DriftingOtter/Project-Resonator/BA Driver Spec Sheets/Knowles_BK_26824/Frequency_Response.png

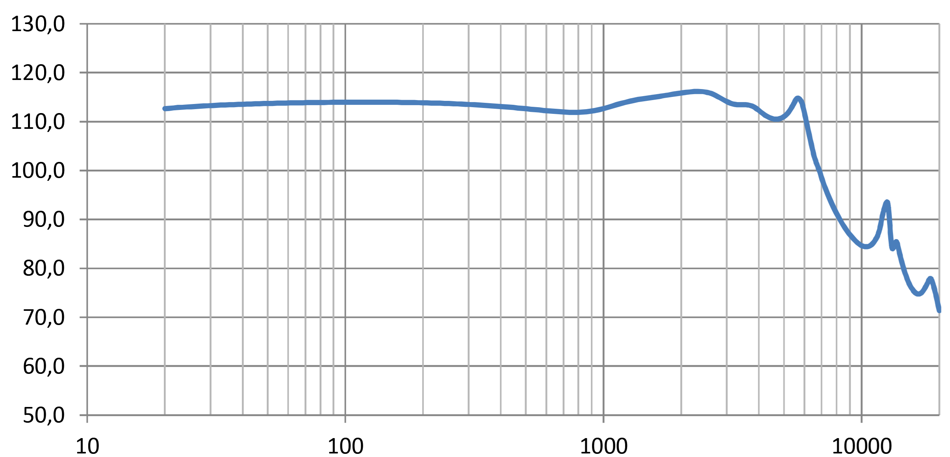
BA Driver Spec Sheets/Knowles_BK_26824/Frequency_Response.png
