DriftingOtter/Project-Resonator/BA Driver Spec Sheets/Knowles_CI_22955/Frequnecy_Response.png

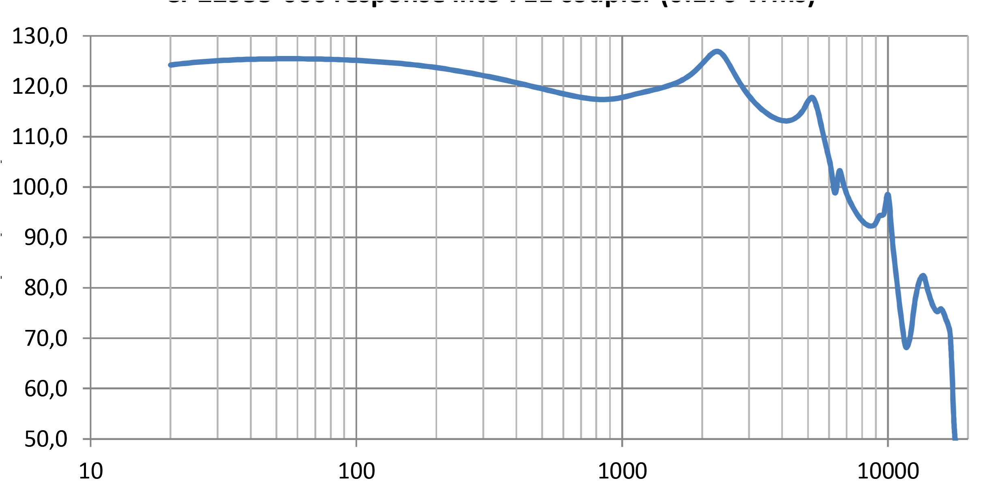
BA Driver Spec Sheets/Knowles_CI_22955/Frequnecy_Response.png
