DriftingOtter/Project-Resonator/BA Driver Spec Sheets/Knowles_CI_22955/Impedence_Response.png

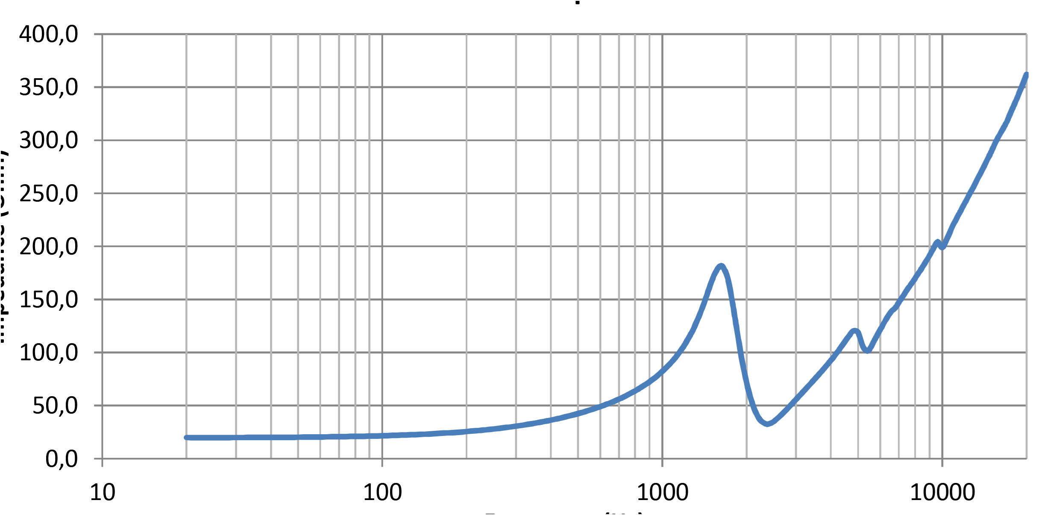
BA Driver Spec Sheets/Knowles_CI_22955/Impedence_Response.png
