DriftingOtter/Project-Resonator/BA Driver Spec Sheets/Knowles_ED_30262/Frequnecy_Response.png

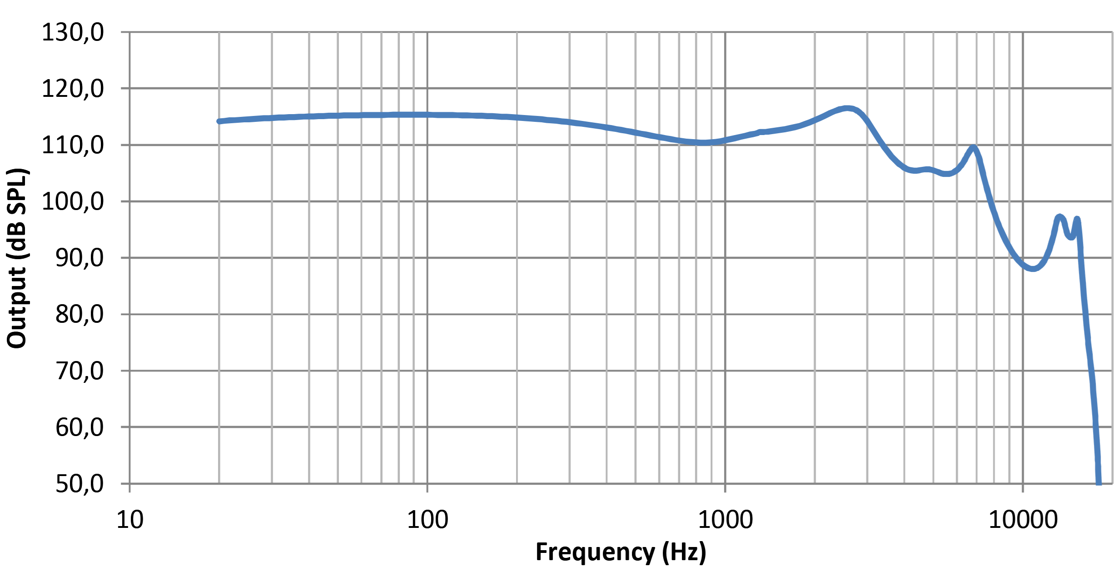
BA Driver Spec Sheets/Knowles_ED_30262/Frequnecy_Response.png
