DriftingOtter/Project-Resonator/BA Driver Spec Sheets/Knowles_HODVTEC-31618/Impedence_Response.png

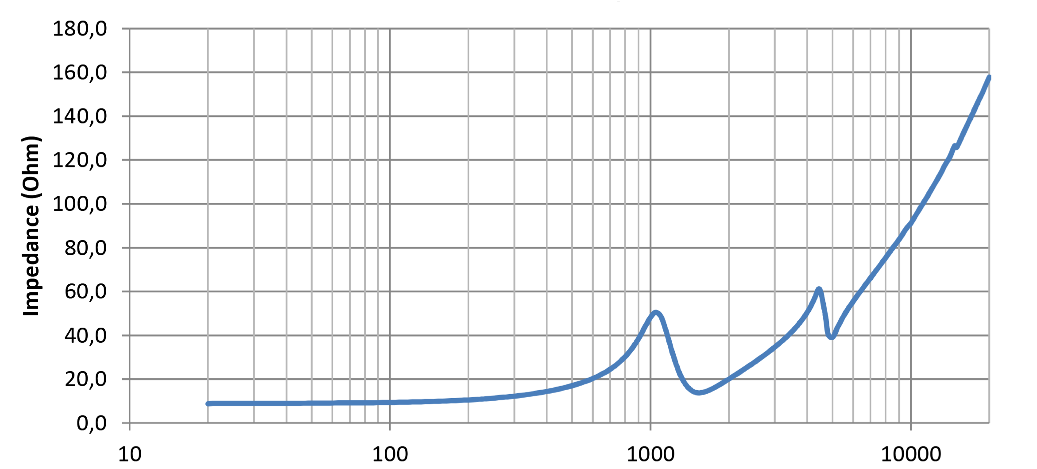
BA Driver Spec Sheets/Knowles_HODVTEC-31618/Impedence_Response.png
