DriftingOtter/Project-Resonator/BA Driver Spec Sheets/Knowles_RDI_34006/Frequnecy_Response.png

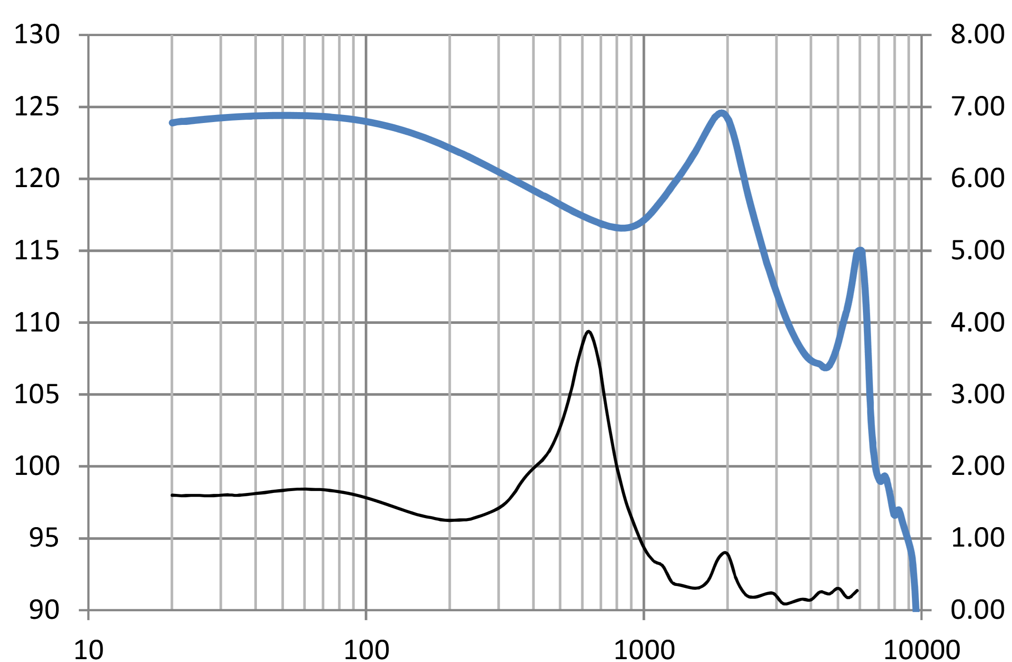
BA Driver Spec Sheets/Knowles_RDI_34006/Frequnecy_Response.png
