DriftingOtter/Project-Resonator/BA Driver Spec Sheets/Knowles_SR6438NWS/Frequnecy_Response.png

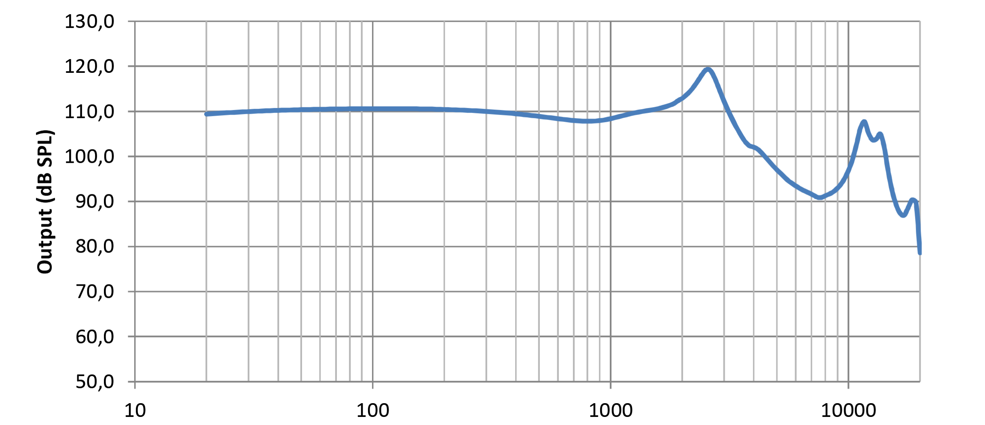
BA Driver Spec Sheets/Knowles_SR6438NWS/Frequnecy_Response.png
