DriftingOtter/Project-Resonator/BA Driver Spec Sheets/Knowles_TEC_30033/Frequnecy_Response.png

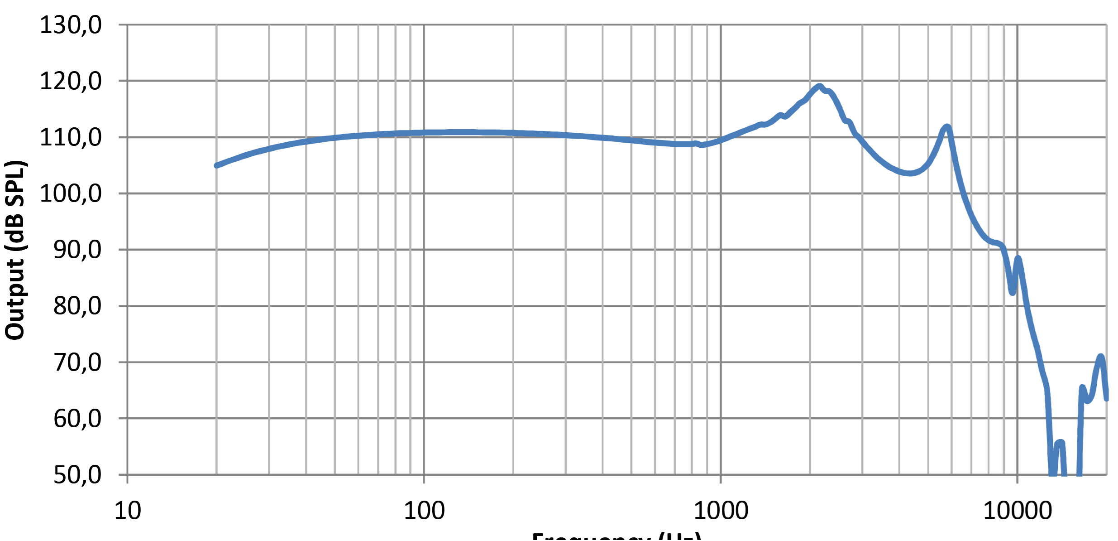
BA Driver Spec Sheets/Knowles_TEC_30033/Frequnecy_Response.png
