DriftingOtter/Project-Resonator/BA Driver Spec Sheets/Knowles_TEC_30033/Impedence_Response.png

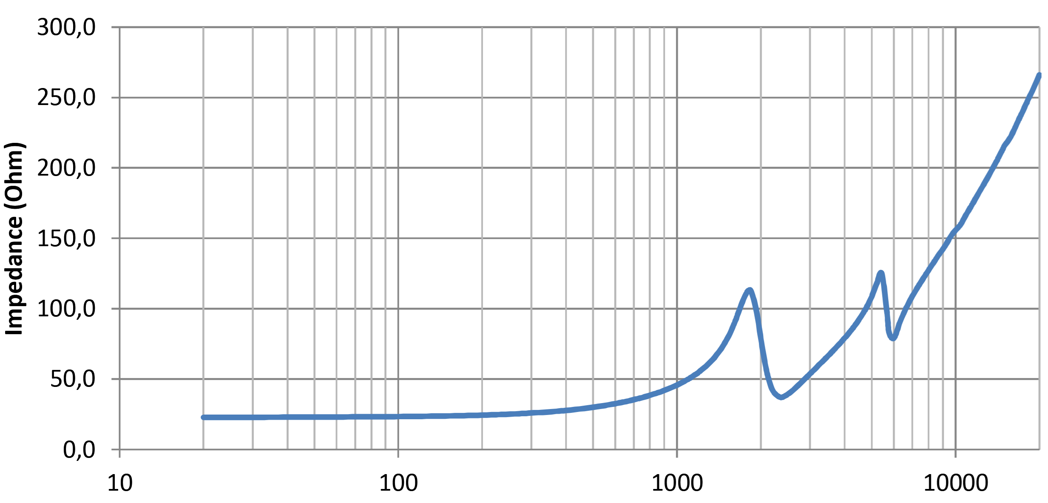
BA Driver Spec Sheets/Knowles_TEC_30033/Impedence_Response.png
