DriftingOtter/Project-Resonator/BA Driver Spec Sheets/Knowles_TWFK_30017/Impedence_Response.png

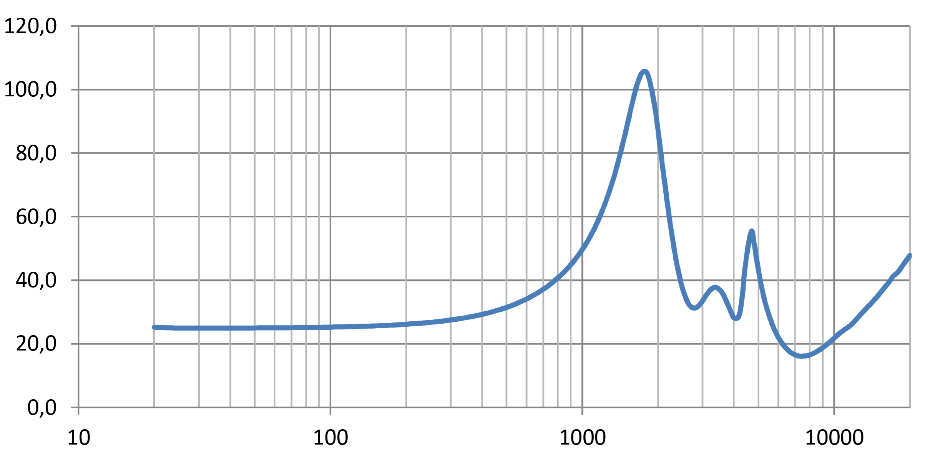
BA Driver Spec Sheets/Knowles_TWFK_30017/Impedence_Response.png
