DriftingOtter/Project-Resonator/BA Driver Spec Sheets/Sonion_38D1XJ007Mi8a/Frequency_Response.png

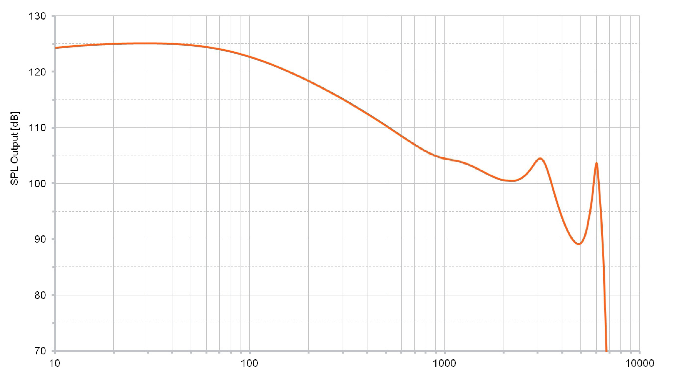
BA Driver Spec Sheets/Sonion_38D1XJ007Mi8a/Frequency_Response.png
