DriftingOtter/Project-Resonator/Mock Prototype Images/8_20_25__FRONT_CENTER_SPLIT_VIEW.png

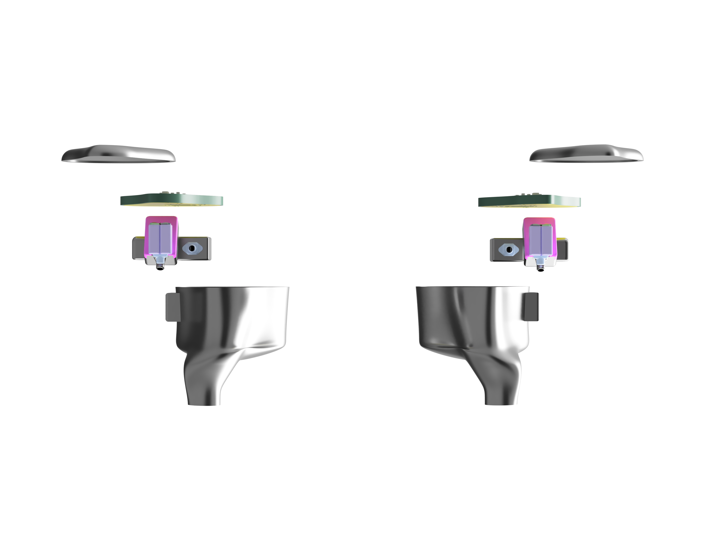
Mock Prototype Images/8_20_25__FRONT_CENTER_SPLIT_VIEW.png
