DriftingOtter/Project-Resonator/Mock Prototype Images/8_20_25__SIDE_VIEW.png

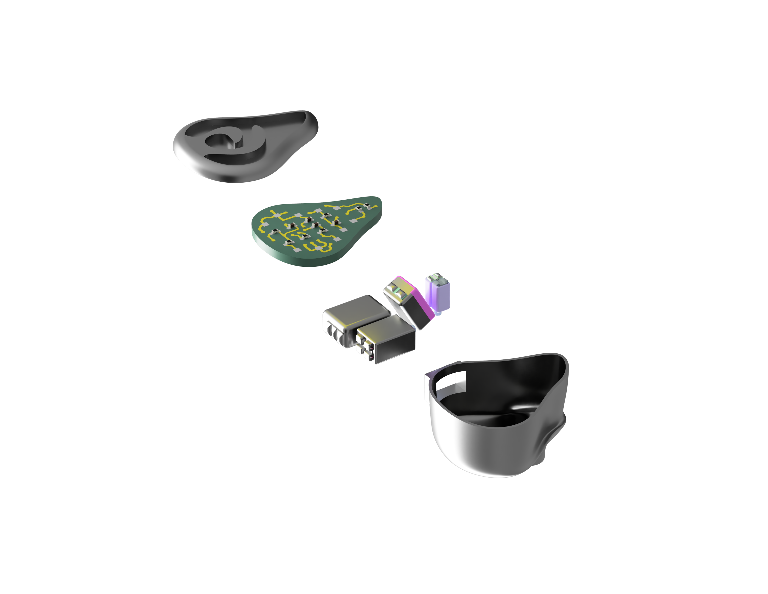
Mock Prototype Images/8_20_25__SIDE_VIEW.png
