DriftingOtter/Project-Resonator/Mock Prototype Images/8_21_25__FLOATING_FRONT_AND_BACK.png

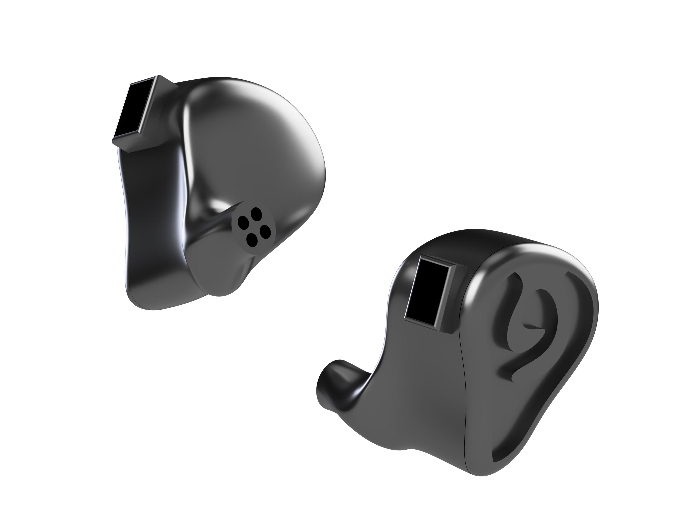
Mock Prototype Images/8_21_25__FLOATING_FRONT_AND_BACK.png
