DriftingOtter/Project-Resonator/Mock Prototype Images/8_21_25__FLOATING_FRONT_VIEW.png

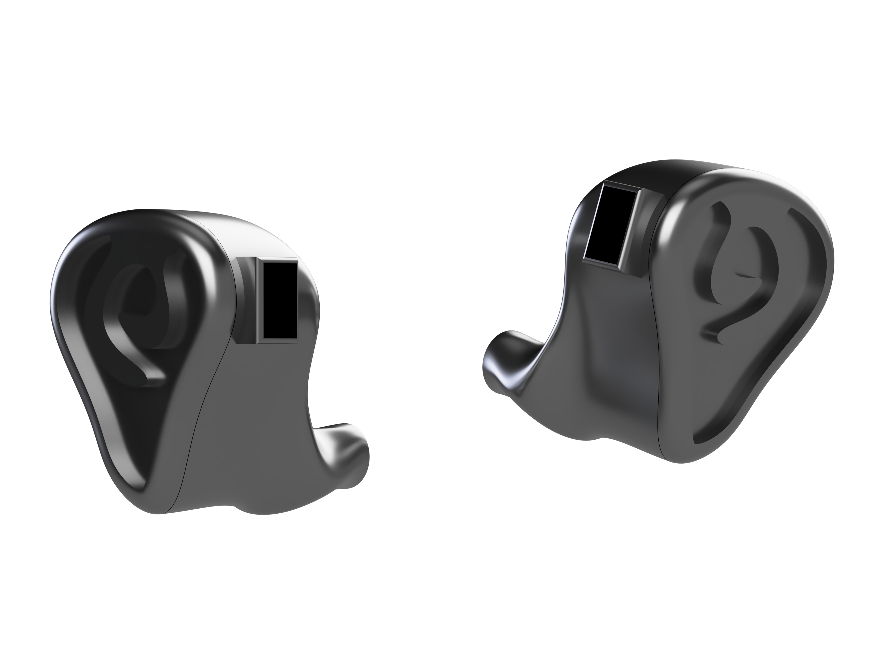
Mock Prototype Images/8_21_25__FLOATING_FRONT_VIEW.png
