DriftingOtter/Project-Resonator/Mock Prototype Images/8_22_25__FLOATING_FRONT_AND_BACK_GOLD.png

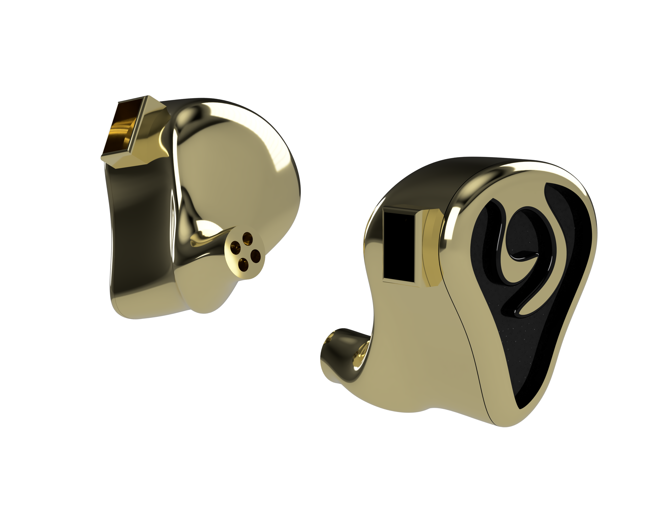
Mock Prototype Images/8_22_25__FLOATING_FRONT_AND_BACK_GOLD.png
