DriftingOtter/Project-Resonator/Mock Prototype Images/8_23_25__FLOATING_FRONT_AND_BACK_CORAL.png

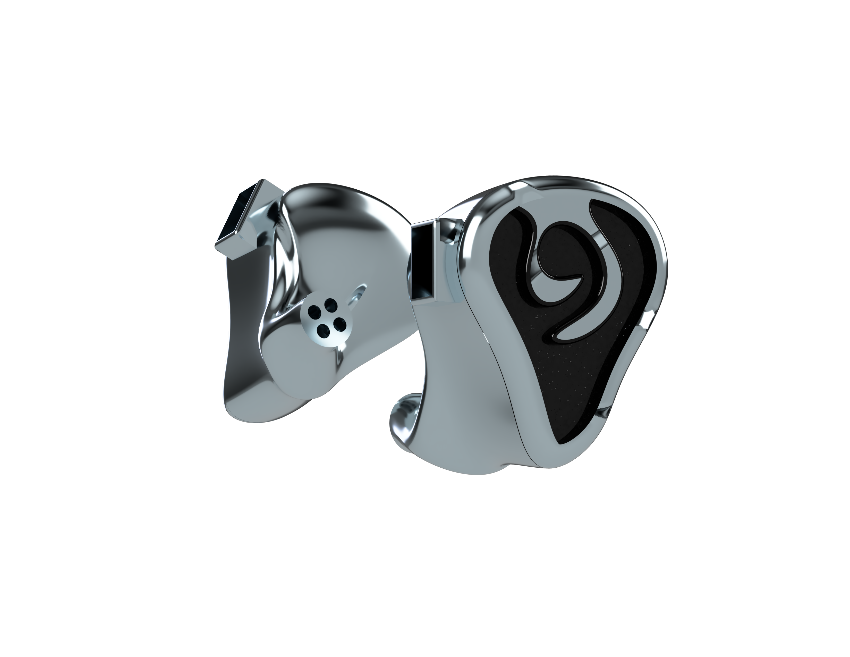
Mock Prototype Images/8_23_25__FLOATING_FRONT_AND_BACK_CORAL.png
