DriftingOtter/Project-Resonator/wiki_assets/Screenshot 2025-12-28 at 7.55.56 PM.png

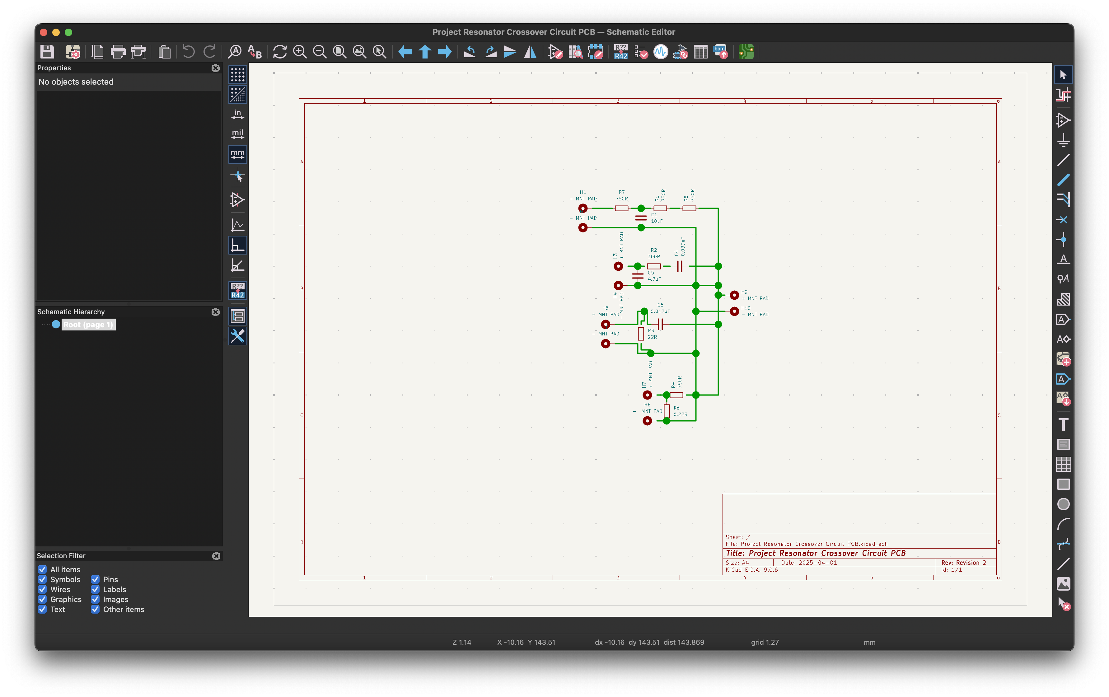
wiki_assets/Screenshot 2025-12-28 at 7.55.56 PM.png
