DriftingOtter/Project-Resonator/wiki_assets/Screenshot 2025-12-28 at 8.12.40 PM.png

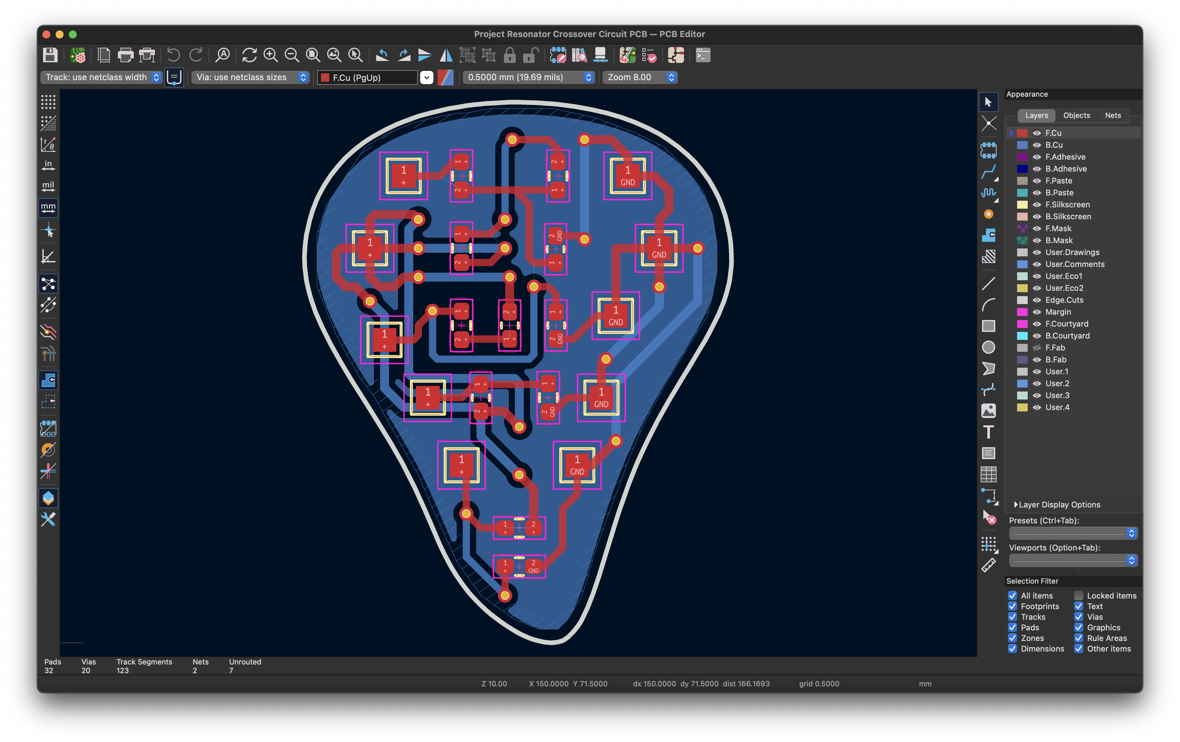
wiki_assets/Screenshot 2025-12-28 at 8.12.40 PM.png
