DriftingOtter/Project-Resonator/wiki_assets/Screenshot 2025-12-28 at 8.13.20 PM.png

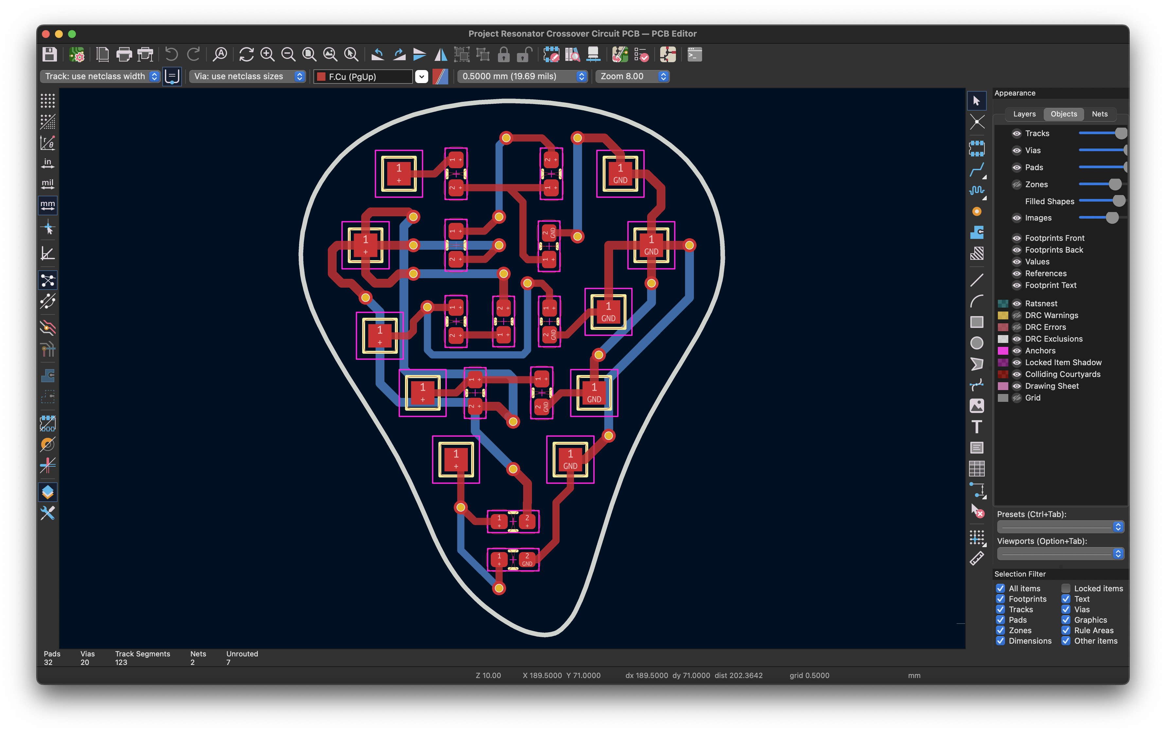
wiki_assets/Screenshot 2025-12-28 at 8.13.20 PM.png
