DriftingOtter/Project-Resonator/wiki_assets/Screenshot 2025-12-28 at 8.16.02 PM.png

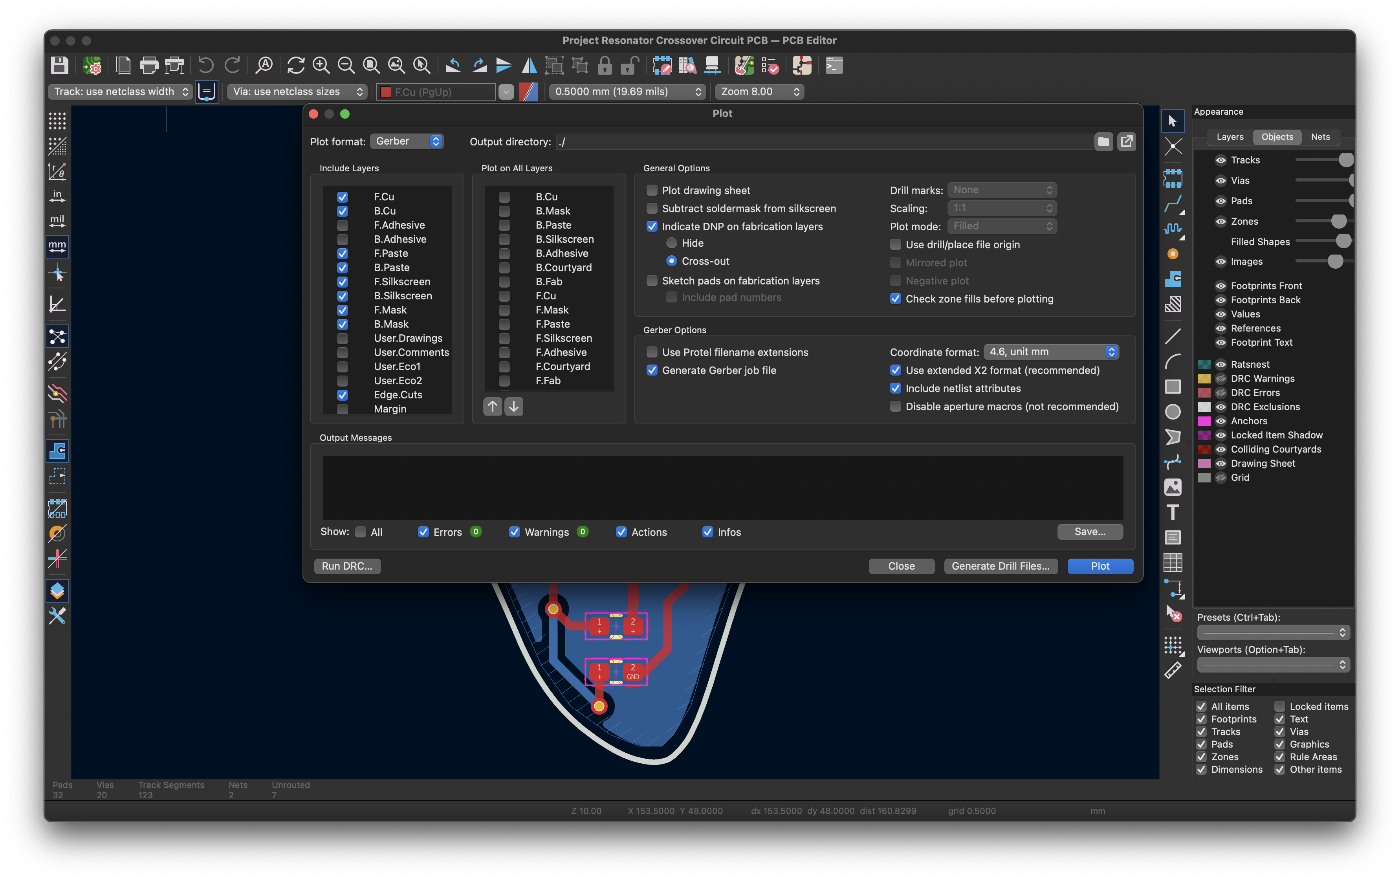
wiki_assets/Screenshot 2025-12-28 at 8.16.02 PM.png
