DriftingOtter/Project-Resonator/wiki_assets/Screenshot 2025-12-28 at 10.48.01 PM.png

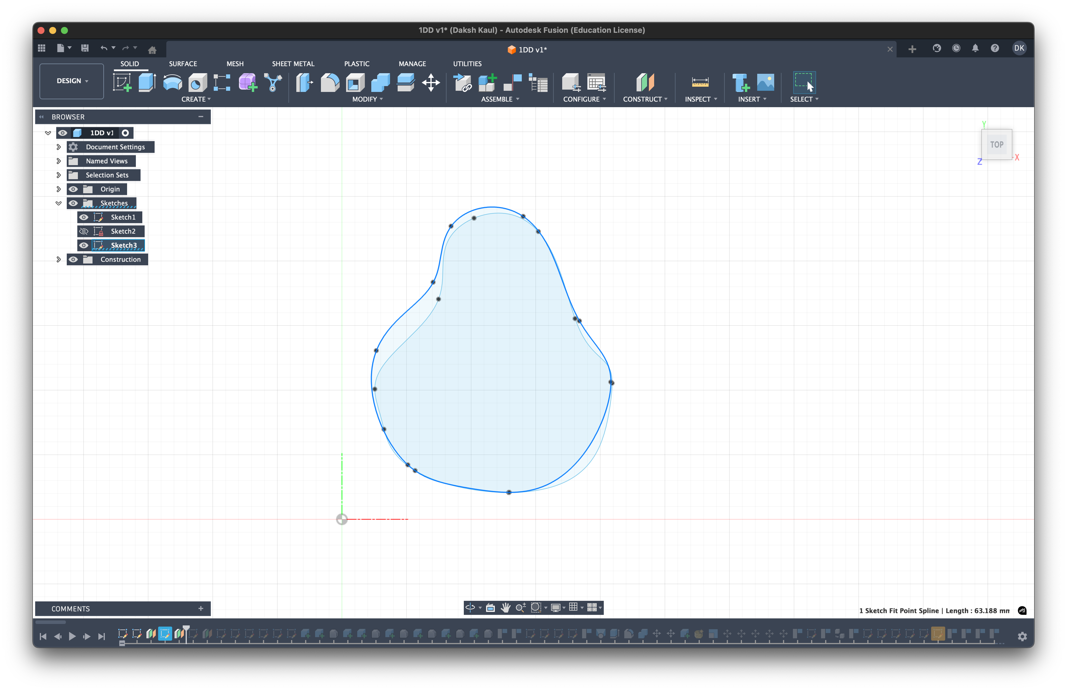
wiki_assets/Screenshot 2025-12-28 at 10.48.01 PM.png
