DriftingOtter/Project-Resonator/wiki_assets/Screenshot 2025-12-28 at 10.58.05 PM.png

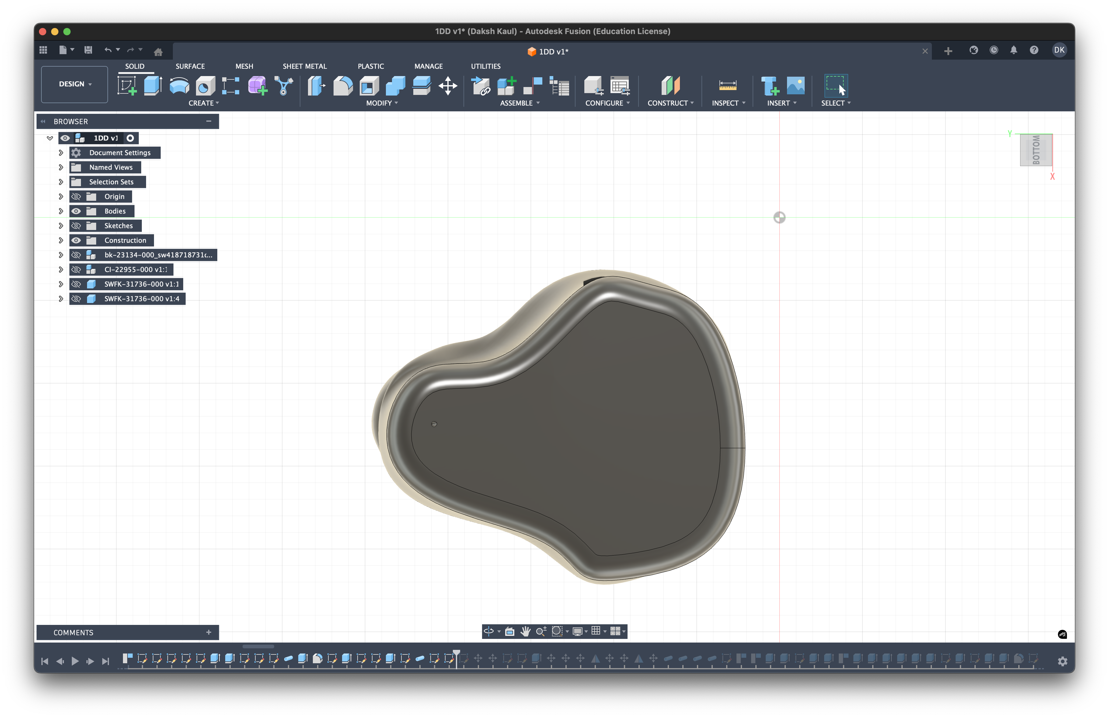
wiki_assets/Screenshot 2025-12-28 at 10.58.05 PM.png
